Raffa2s/T1ny_bl0om/Images/photo_2019-07-17_12-13-22.jpg

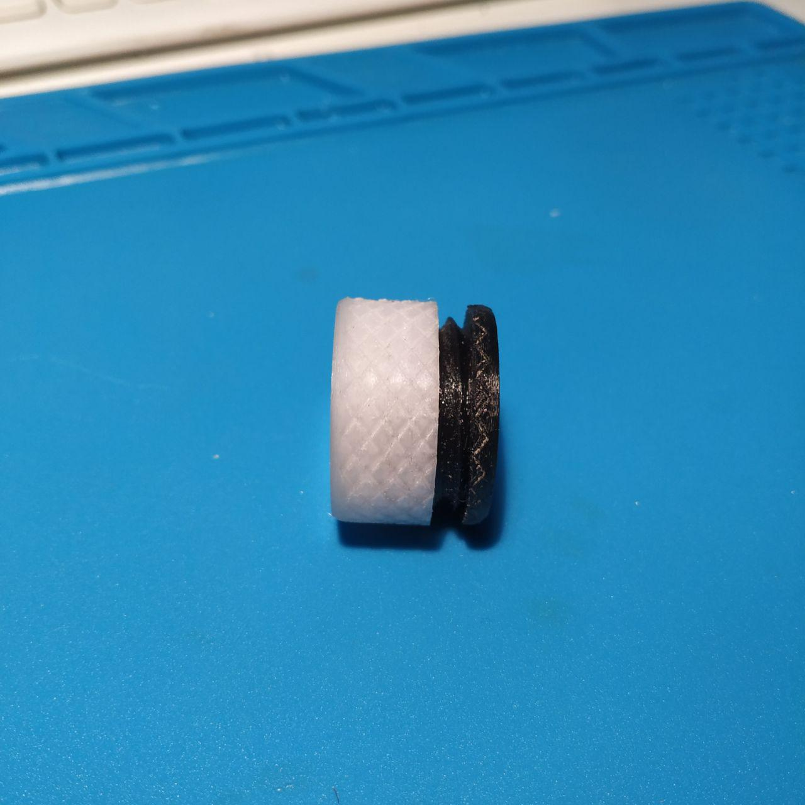
Images/photo_2019-07-17_12-13-22.jpg
