Raffa2s/T1ny_bl0om/Images/photo_2019-07-17_15-17-39.jpg

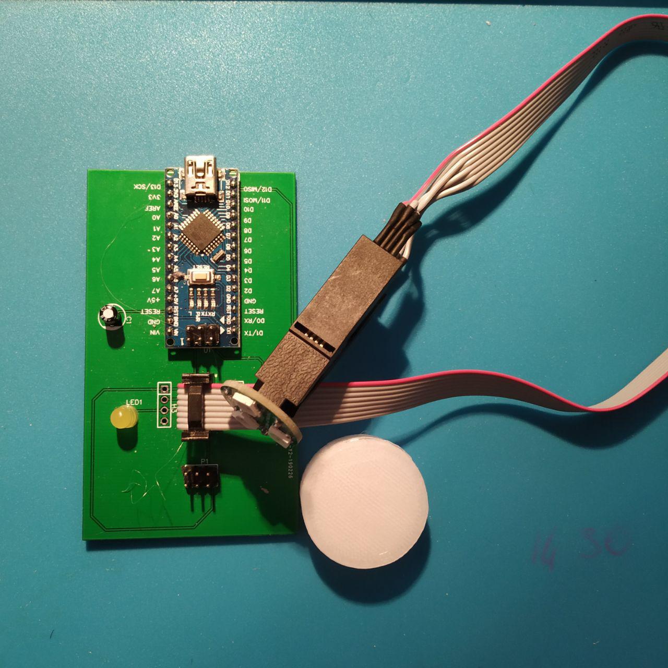
Images/photo_2019-07-17_15-17-39.jpg
