Raffa2s/T1ny_bl0om/Images/photo_2019-07-18_10-05-11.jpg

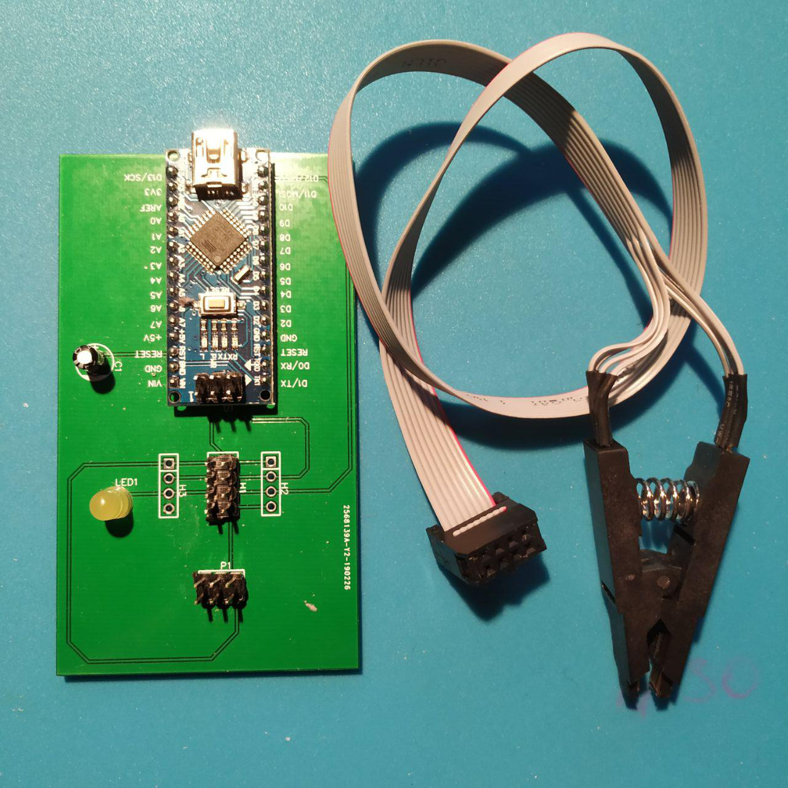
Images/photo_2019-07-18_10-05-11.jpg
