Raffa2s/T1ny_bl0om/Images/photo_2019-07-18_10-40-03.jpg

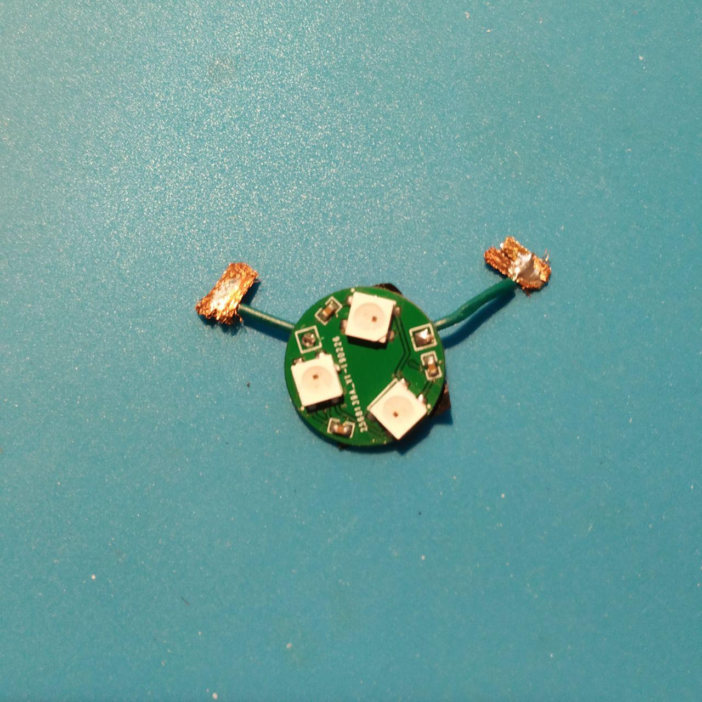
Images/photo_2019-07-18_10-40-03.jpg
