Raffa2s/T1ny_bl0om/Images/photo_2019-07-18_12-05-26.jpg

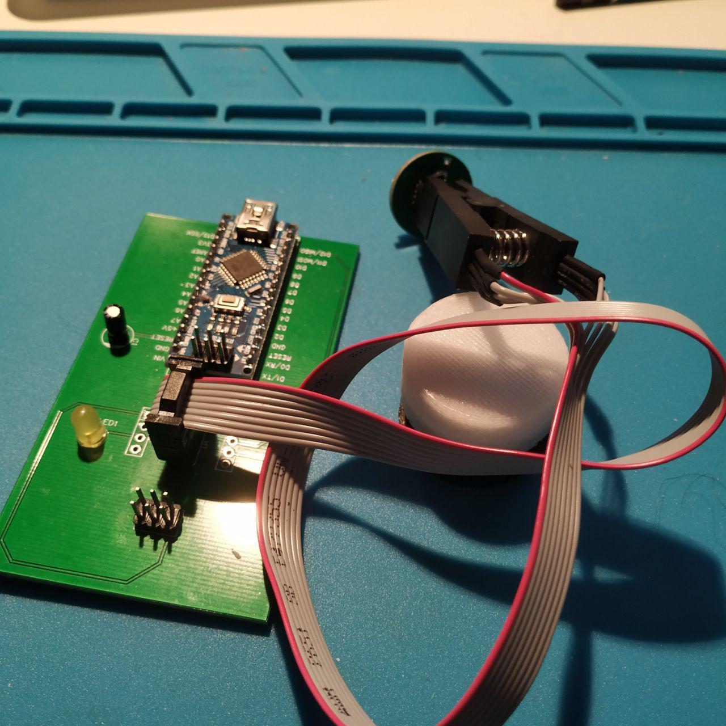
Images/photo_2019-07-18_12-05-26.jpg
